sidereall/eink-desk-dashboard/enclosure/enclosure_body.jpg

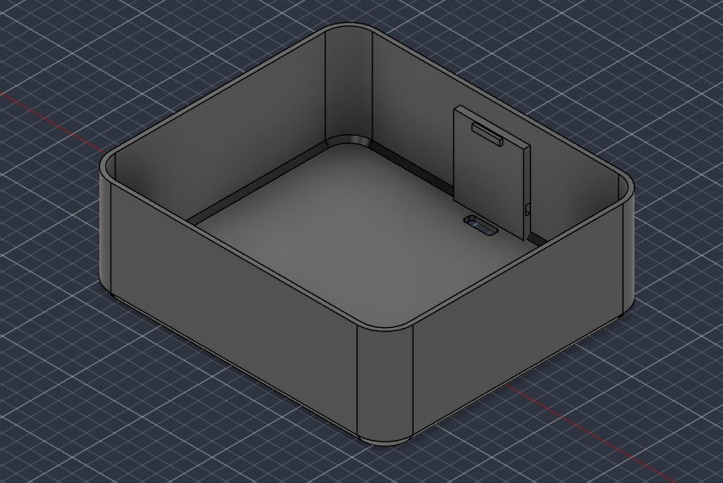
enclosure/enclosure_body.jpg
