sidereall/eink-desk-dashboard/src/icons.h

// icons.h - every bitmap, in one place.
//
// Named <what>_<size>, e.g. icon_rain_48 / icon_rain_96, so a call site can't
// grab the wrong one. Weather icons are ordered to match the WxIcon enum.
//
// Each array has a static_assert on its size. A bitmap must be exactly
// ceil(w/8)*h bytes, or drawBitmap() reads past the end of it.
//
// Include from screens.cpp only. These are `static`, so every extra include
// puts another copy of every array in flash.

#pragma once
#include <Arduino.h> // for PROGMEM
#include <stddef.h>

#define ICON_BYTES(w, h) ((((w) + 7) / 8) * (h))

// INTERFACE -----------------------------------------------------------------------------------------
static const unsigned char PROGMEM icon_wifi[] = { // 16x16
    0x00, 0x00, 0x00, 0x00, 0x1f, 0xf8, 0x3f, 0xfc, 0x60, 0x06, 0xc0, 0x03, 0x87, 0xe1, 0x0f, 0xf0,
    0x18, 0x18, 0x10, 0x08, 0x03, 0xc0, 0x07, 0xe0, 0x04, 0x20, 0x01, 0x80, 0x01, 0x80, 0x00, 0x00};
static_assert(sizeof(icon_wifi) == ICON_BYTES(16, 16), "icon_wifi: wrong byte count");

// Battery, 23x13. Bars drain left to right.
static const unsigned char PROGMEM icon_batt_100[] = {0x3f, 0xff, 0xe0, 0x7f, 0xff, 0xf0, 0xc0, 0x00, 0x18, 0xdd,
                                                      0xdd, 0xd8, 0xdd, 0xdd, 0xde, 0xdd, 0xdd, 0xda, 0xdd, 0xdd,
                                                      0xda, 0xdd, 0xdd, 0xda, 0xdd, 0xdd, 0xde, 0xdd, 0xdd, 0xd8,
                                                      0xc0, 0x00, 0x18, 0x7f, 0xff, 0xf0, 0x3f, 0xff, 0xe0};
static_assert(sizeof(icon_batt_100) == ICON_BYTES(23, 13), "icon_batt_100: wrong byte count");

static const unsigned char PROGMEM icon_batt_75[] = {0x3f, 0xff, 0xe0, 0x7f, 0xff, 0xf0, 0xc0, 0x00, 0x18, 0xdd,
                                                     0xdc, 0x18, 0xdd, 0xdc, 0x1e, 0xdd, 0xdc, 0x1a, 0xdd, 0xdc,
                                                     0x1a, 0xdd, 0xdc, 0x1a, 0xdd, 0xdc, 0x1e, 0xdd, 0xdc, 0x18,
                                                     0xc0, 0x00, 0x18, 0x7f, 0xff, 0xf0, 0x3f, 0xff, 0xe0};
static_assert(sizeof(icon_batt_75) == ICON_BYTES(23, 13), "icon_batt_75: wrong byte count");

static const unsigned char PROGMEM icon_batt_50[] = {0x3f, 0xff, 0xe0, 0x7f, 0xff, 0xf0, 0xc0, 0x00, 0x18, 0xdd,
                                                     0xc0, 0x18, 0xdd, 0xc0, 0x1e, 0xdd, 0xc0, 0x1a, 0xdd, 0xc0,
                                                     0x1a, 0xdd, 0xc0, 0x1a, 0xdd, 0xc0, 0x1e, 0xdd, 0xc0, 0x18,
                                                     0xc0, 0x00, 0x18, 0x7f, 0xff, 0xf0, 0x3f, 0xff, 0xe0};
static_assert(sizeof(icon_batt_50) == ICON_BYTES(23, 13), "icon_batt_50: wrong byte count");

static const unsigned char PROGMEM icon_batt_25[] = {0x3f, 0xff, 0xe0, 0x7f, 0xff, 0xf0, 0xc0, 0x00, 0x18, 0xdc,
                                                     0x00, 0x18, 0xdc, 0x00, 0x1e, 0xdc, 0x00, 0x1a, 0xdc, 0x00,
                                                     0x1a, 0xdc, 0x00, 0x1a, 0xdc, 0x00, 0x1e, 0xdc, 0x00, 0x18,
                                                     0xc0, 0x00, 0x18, 0x7f, 0xff, 0xf0, 0x3f, 0xff, 0xe0};
static_assert(sizeof(icon_batt_25) == ICON_BYTES(23, 13), "icon_batt_25: wrong byte count");

static const unsigned char PROGMEM icon_batt_0[] = {0x3f, 0xff, 0xe0, 0x7f, 0xff, 0xf0, 0xc0, 0x00, 0x18, 0xc0,
                                                    0x00, 0x18, 0xc0, 0x00, 0x1e, 0xc0, 0x00, 0x1a, 0xc0, 0x00,
                                                    0x1a, 0xc0, 0x00, 0x1a, 0xc0, 0x00, 0x1e, 0xc0, 0x00, 0x18,
                                                    0xc0, 0x00, 0x18, 0x7f, 0xff, 0xf0, 0x3f, 0xff, 0xe0};
static_assert(sizeof(icon_batt_0) == ICON_BYTES(23, 13), "icon_batt_0: wrong byte count");

static const unsigned char PROGMEM icon_degree_small[] = { // 16x10
    0x73, 0xff, 0x8b, 0xff, 0x8b, 0x00, 0x8b, 0x00, 0x73, 0x00,
    0x03, 0x00, 0x03, 0x00, 0x03, 0x00, 0x03, 0xff, 0x03, 0xff};
static_assert(sizeof(icon_degree_small) == ICON_BYTES(16, 10), "icon_degree_small: wrong byte count");

static const unsigned char PROGMEM icon_degree_f_small[] = { // 16x10
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
    0xf0, 0x00, 0x00, 0x00, 0x00, 0x00, 0xf0, 0x00, 0xf0, 0x00, 0xf0, 0x00, 0xf0, 0x00, 0x00, 0x00, 0x00, 0x00, 0xf0,
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
static_assert(sizeof(icon_snow_96) == ICON_BYTES(96, 96), "icon_snow_96: wrong byte count");
