sidereall/eink-desk-dashboard/src/timezones.h

// timezones.h - the list for the timezone picker.
//
// These are POSIX TZ strings, not plain offsets. An offset like "+1" is wrong
// for half the year; a POSIX string carries the DST rules too:
//
//     CET-1CEST,M3.5.0,M10.5.0/3
//     |    |     |          `-- back, last Sunday of October, 03:00
//     |    |     `------------- forward, last Sunday of March
//     |    `------------------- summer name
//     `------------------------ standard name, 1h east of UTC
//
// localtime_r() applies those rules itself, so DST works with no network.
//
// Included by web_ui.cpp only - it's static, so each include is another copy.
#pragma once
#include <stddef.h>

struct TimeZoneEntry {
  const char *label; // what the dropdown shows
  const char *posix; // the DST rules the clock applies
};

static const TimeZoneEntry TIMEZONES[] = {
    {"UTC", "UTC0"},

    {"Europe/London", "GMT0BST,M3.5.0/1,M10.5.0"},
    {"Europe/Lisbon", "WET0WEST,M3.5.0/1,M10.5.0"},
    {"Europe/Madrid", "CET-1CEST,M3.5.0,M10.5.0/3"},
    {"Europe/Paris", "CET-1CEST,M3.5.0,M10.5.0/3"},
    {"Europe/Amsterdam", "CET-1CEST,M3.5.0,M10.5.0/3"},
    {"Europe/Berlin", "CET-1CEST,M3.5.0,M10.5.0/3"},
    {"Europe/Zurich", "CET-1CEST,M3.5.0,M10.5.0/3"},
    {"Europe/Vienna", "CET-1CEST,M3.5.0,M10.5.0/3"},
    {"Europe/Rome", "CET-1CEST,M3.5.0,M10.5.0/3"},
    {"Europe/Prague", "CET-1CEST,M3.5.0,M10.5.0/3"},
    {"Europe/Warsaw", "CET-1CEST,M3.5.0,M10.5.0/3"},
    {"Europe/Budapest", "CET-1CEST,M3.5.0,M10.5.0/3"},
    {"Europe/Stockholm", "CET-1CEST,M3.5.0,M10.5.0/3"},
    {"Europe/Oslo", "CET-1CEST,M3.5.0,M10.5.0/3"},
    {"Europe/Copenhagen", "CET-1CEST,M3.5.0,M10.5.0/3"},
    {"Europe/Helsinki", "EET-2EEST,M3.5.0/3,M10.5.0/4"},
    {"Europe/Athens", "EET-2EEST,M3.5.0/3,M10.5.0/4"},
    {"Europe/Bucharest", "EET-2EEST,M3.5.0/3,M10.5.0/4"},
    {"Europe/Kyiv", "EET-2EEST,M3.5.0/3,M10.5.0/4"},
    {"Europe/Riga", "EET-2EEST,M3.5.0/3,M10.5.0/4"},
    {"Europe/Vilnius", "EET-2EEST,M3.5.0/3,M10.5.0/4"},
    {"Europe/Tallinn", "EET-2EEST,M3.5.0/3,M10.5.0/4"},
    {"Europe/Istanbul", "<+03>-3"},
    {"Europe/Moscow", "MSK-3"},

    {"America/New_York", "EST5EDT,M3.2.0,M11.1.0"},
    {"America/Toronto", "EST5EDT,M3.2.0,M11.1.0"},
    {"America/Chicago", "CST6CDT,M3.2.0,M11.1.0"},
    {"America/Denver", "MST7MDT,M3.2.0,M11.1.0"},
    {"America/Phoenix", "MST7"},
    {"America/Los_Angeles", "PST8PDT,M3.2.0,M11.1.0"},
    {"America/Vancouver", "PST8PDT,M3.2.0,M11.1.0"},
    {"America/Anchorage", "AKST9AKDT,M3.2.0,M11.1.0"},
    {"America/Mexico_City", "CST6"},
    {"America/Sao_Paulo", "<-03>3"},

    {"Asia/Jerusalem", "IST-2IDT,M3.4.4/26,M10.5.0"},
    {"Asia/Dubai", "<+04>-4"},
    {"Asia/Karachi", "PKT-5"},
    {"Asia/Kolkata", "IST-5:30"},
    {"Asia/Bangkok", "<+07>-7"},
    {"Asia/Shanghai", "CST-8"},
    {"Asia/Singapore", "<+08>-8"},
    {"Asia/Hong_Kong", "HKT-8"},
    {"Asia/Tokyo", "JST-9"},
    {"Asia/Seoul", "KST-9"},

    {"Australia/Perth", "AWST-8"},
    {"Australia/Brisbane", "AEST-10"},
    {"Australia/Adelaide", "ACST-9:30ACDT,M10.1.0,M4.1.0/3"},
    {"Australia/Sydney", "AEST-10AEDT,M10.1.0,M4.1.0/3"},
    {"Pacific/Auckland", "NZST-12NZDT,M9.5.0,M4.1.0/3"},
};

static const size_t TIMEZONE_COUNT = sizeof(TIMEZONES) / sizeof(TIMEZONES[0]);
